ondras12345/electricity-meter/src/datalogger.cpp

#include "datalogger.h"
#include <Arduino.h>
#include <SerialFlash.h>
#include "hardware.h"
#include "pulse_counter.h"
#include "rtc.h"
#include "debug.h"


static uint_fast8_t datalogger_current_file_index = -1;  // -1 means invalid
static uint32_t datalogger_current_index = 0;


static bool ensure_erasable_file(const char * filename, uint32_t length)
{
    if (SerialFlash.exists(filename))
        return true;

    DEBUG->print("Creating file: ");
    DEBUG->print(filename);
    DEBUG->print(" ... ");
    if (!SerialFlash.createErasable(filename, length))
    {
        DEBUG->println("failed");
        return false;
    }
    DEBUG->println("OK");
    return true;
}


const char * datalogger_file_number_to_filename(uint_fast8_t i)
{
    static char filename[3];
    if (i >= DATALOGGER_FILE_COUNT) return "invalid";
    snprintf(filename, sizeof filename, "%02u", i);
    return filename;
}


bool datalogger_record_empty(datalogger_record_t record)
{
    // SPI flash initializes to all 0xFF, so an empty record
    // should be all FF. pulses == 0xFFFF is not a valid pulse count,
    // so we can test that.
    return record.pulses == 0xFFFF;
}


static void write_record(datalogger_record_t record)
{
    // cppcheck-suppress[knownConditionTrueFalse] false positive
    if (datalogger_current_file_index == (uint_fast8_t)-1)
    {
        // no valid file
        DEBUG->println("error: no file to log to");
        return;
    }

    // prevent invalid pulse count
    if (record.pulses == (uint16_t)-1) record.pulses = 0;

    DEBUG->print("datalogger record: timestamp=");
    DEBUG->print(record.timestamp);
    DEBUG->print(" pulses=");
    DEBUG->println(record.pulses);

    // We need to erase next file BEFORE writing last record.
    // If power failed while writing, we need to be able to find one file
    // where the last record is invalid.
    uint_fast8_t next_file = (datalogger_current_file_index + 1) % DATALOGGER_FILE_COUNT;
    bool is_last_record = datalogger_current_index == DATALOGGER_FILE_RECORDS - 1;
    if (is_last_record)
    {
        const char * filename = datalogger_file_number_to_filename(next_file);
        DEBUG->print("erasing next file: ");
        DEBUG->println(filename);
        SerialFlashFile f = SerialFlash.open(filename);
        if (!f)
        {
            DEBUG->println("error: could not open");
            // let's try again next time...
            return;
        }
        f.erase();
    }
    SerialFlashFile f = SerialFlash.open(datalogger_file_number_to_filename(datalogger_current_file_index));
    f.seek(datalogger_current_index * sizeof(datalogger_record_t));
    f.write(&record, sizeof record);
    datalogger_current_index++;
    if (is_last_record)
    {
        datalogger_current_index = 0;
        datalogger_current_file_index = next_file;
    }
}


void datalogger_init()
{
    DEBUG->print("Flash init: ");
    DEBUG->println(SerialFlash.begin(PIN_SPI_SS_FLASH));

    DEBUG->println("creating files...");
    bool error = false;
    for (uint_fast8_t i = 0; i < DATALOGGER_FILE_COUNT; i++)
    {
        if (!ensure_erasable_file(datalogger_file_number_to_filename(i), DATALOGGER_FILE_LENGTH))
        {
            error = true;
            break;
        }
    }

    // Not trying to erase flash on error to prevent data loss.
    if (error)
    {
        DEBUG->println("Critical: failed to create file");
        // If this ever happens, you should try to erase the chip.
        return;
    }

    DEBUG->println("searching for last record");
    // Read the last record of each file, search for empty record.
    // We are only doing this once at startup, and there aren't that many
    // files. It should be OK to just open & read each one.
    uint_fast8_t current_file = -1;
    SerialFlashFile f;
    for (uint_fast8_t i = 0; i < DATALOGGER_FILE_COUNT; i++)
    {
        const char * filename = datalogger_file_number_to_filename(i);
        DEBUG->print("file: ");
        DEBUG->println(filename);
        f = SerialFlash.open(filename);
        if (!f)
        {
            // This should never happen, we called ensure_erasable_file before.
            DEBUG->println("error: file does not exist");
            continue;
        }
        datalogger_record_t last_record;
        f.seek((DATALOGGER_FILE_RECORDS - 1) * sizeof(last_record));
        f.read(&last_record, sizeof last_record);
        if (datalogger_record_empty(last_record))
        {
            DEBUG->println("empty at the end");
            current_file = i;
            break;
        }
        // SerialFlash files are not real files, no need to close()
    }

    if (!f)
    {
        DEBUG->println("error: current_file does not exist");
        return;
    }

    datalogger_current_file_index = current_file;

    // Binary search within current_file
    uint32_t left = 0;
    uint32_t right = DATALOGGER_FILE_RECORDS - 1;
    uint32_t last_valid = -1;
    while (left <= right)
    {
        DEBUG->print("l=");
        DEBUG->print(left);
        DEBUG->print(" r=");
        DEBUG->println(right);
        uint32_t mid = (left + right) / 2;
        datalogger_record_t record;
        f.seek(mid * sizeof(record));
        f.read(&record, sizeof(record));
        if (!datalogger_record_empty(record))
        {
            last_valid = mid;
            left = mid+1;
        }
        else
        {
            if (right == 0) break;
            right = mid-1;
        }
    }
    // If no valid record was found, last_valid was initialized to
    // (uint32_t)(-1), so last_valid+1 == 0 and everything still works.
    datalogger_current_index = last_valid+1;
    DEBUG->print("datalogger_current_index=");
    DEBUG->println(datalogger_current_index);
}


void datalogger_loop()
{
    static unsigned long prev_millis = 0;
    unsigned long now = millis();
    bool too_early = now - prev_millis <= 1500UL;
    bool too_late = now - prev_millis >= 62000UL;
    if ((rtc_time.second() == 0 && !too_early) || too_late)
    {
        prev_millis = now;
        datalogger_record_t record;
        record.timestamp = rtc_time.secondstime();
        uint32_t pulses = pulse_counter_get_count();
        static uint32_t prev_pulses = 0;
        record.pulses = pulses-prev_pulses;
        prev_pulses=pulses;
        write_record(record);
    }
}
